marknzl/RoboticsYear13/3D Designs/models/Pallet.SLDPRT

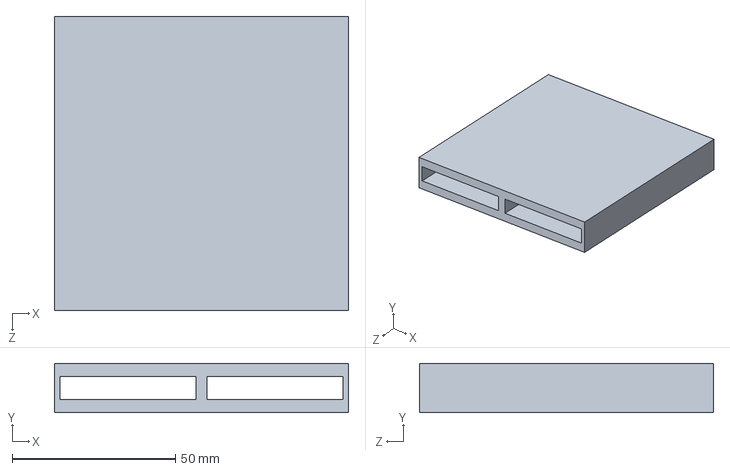
[picture p22: CAD file, 2021-07-02]
3D Designs/models/Pallet.SLDPRT
90.0 x 15.0 x 90.0 mm
