marknzl/RoboticsYear13/3D Designs/models/Pulley mount.SLDPRT

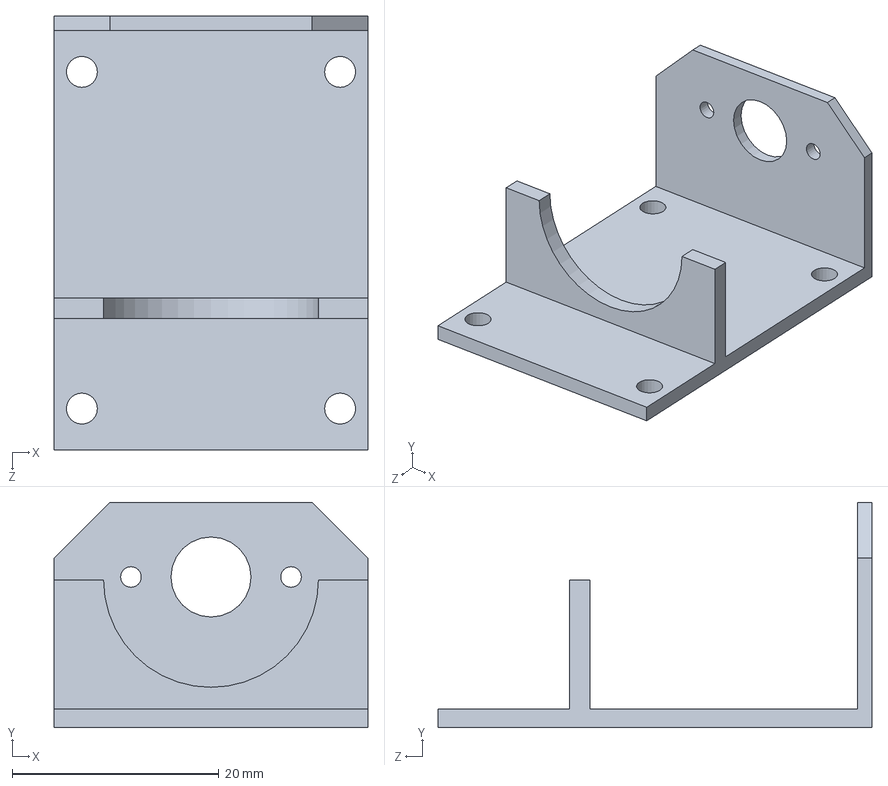
[picture p23: CAD file, 2021-07-02]
3D Designs/models/Pulley mount.SLDPRT
30.4 x 21.8 x 42.0 mm
