marknzl/RoboticsYear13/3D Designs/models/Motor.SLDPRT

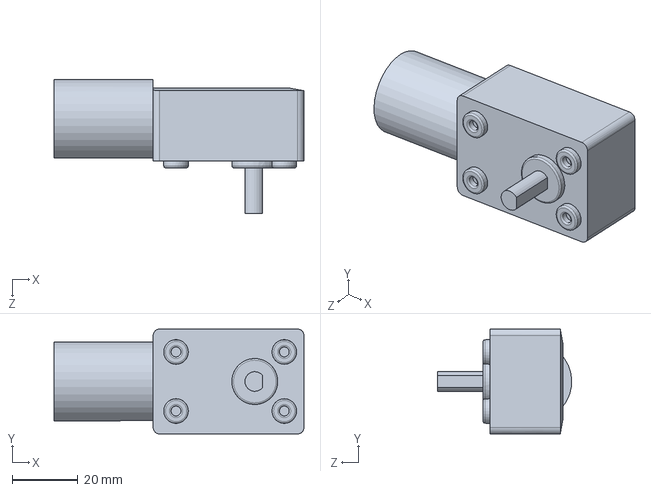
[picture p24: CAD file, 2021-07-02]
3D Designs/models/Motor.SLDPRT
76.2 x 32.0 x 41.0 mm
