marknzl/RoboticsYear13/3D Designs/models/Limit switch trigger.SLDPRT

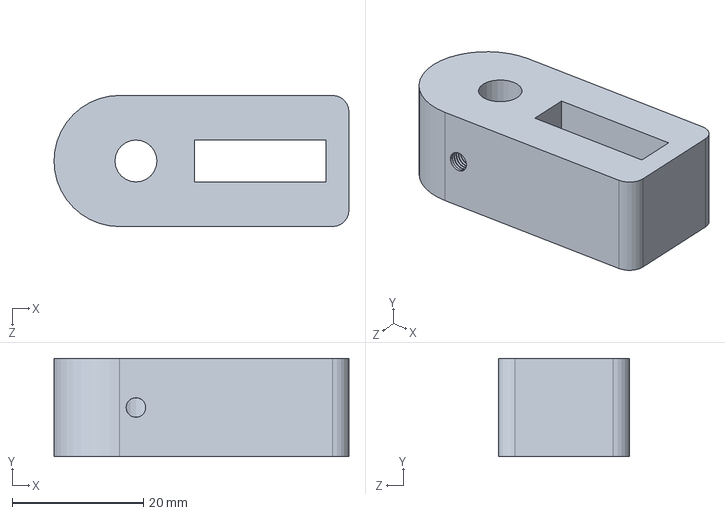
[picture p25: CAD file, 2021-07-02]
3D Designs/models/Limit switch trigger.SLDPRT
45.0 x 15.0 x 20.0 mm
