marknzl/RoboticsYear13/3D Designs/models/Timing belt fastener.SLDPRT

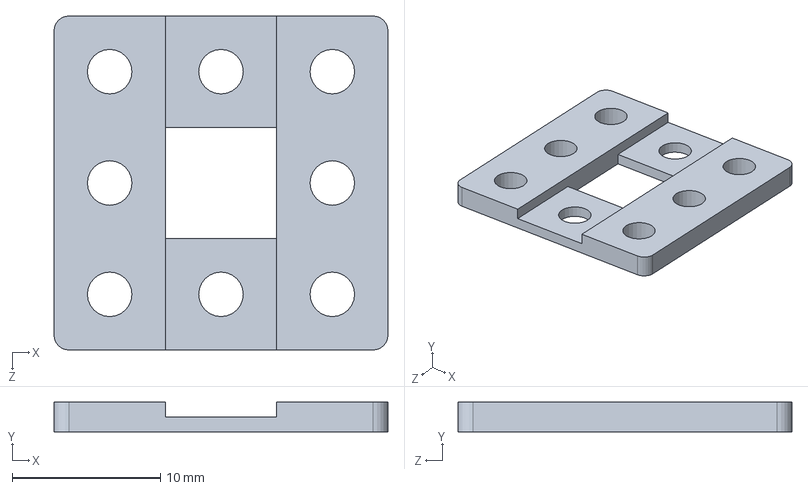
[picture p26: CAD file, 2021-07-02]
3D Designs/models/Timing belt fastener.SLDPRT
22.5 x 2.00 x 22.5 mm
