marknzl/RoboticsYear13/3D Designs/models/Motor clip - left (New).SLDPRT

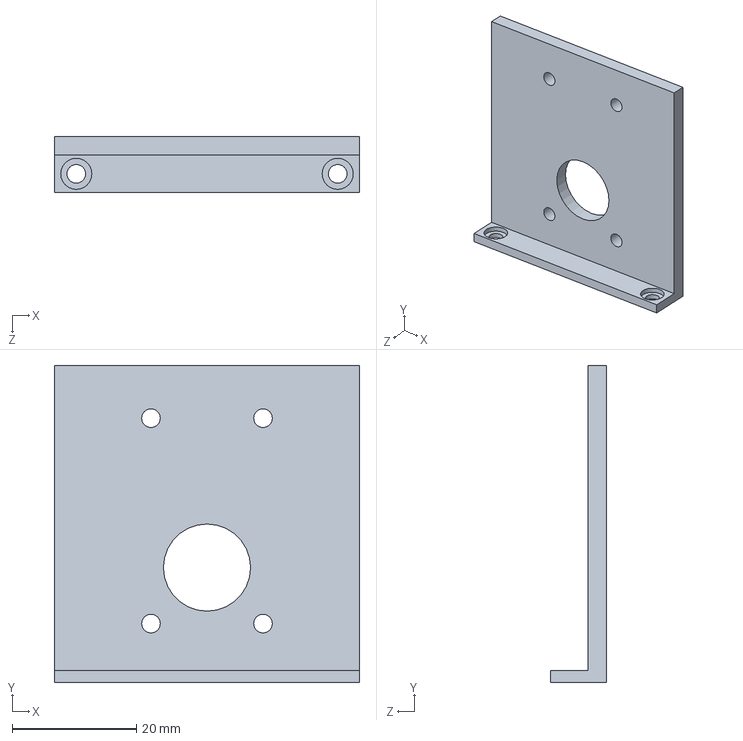
[picture p27: CAD file, 2021-07-02]
3D Designs/models/Motor clip - left (New).SLDPRT
49.0 x 51.0 x 9.00 mm
