marknzl/RoboticsYear13/3D Designs/models/Wheel (New).SLDPRT

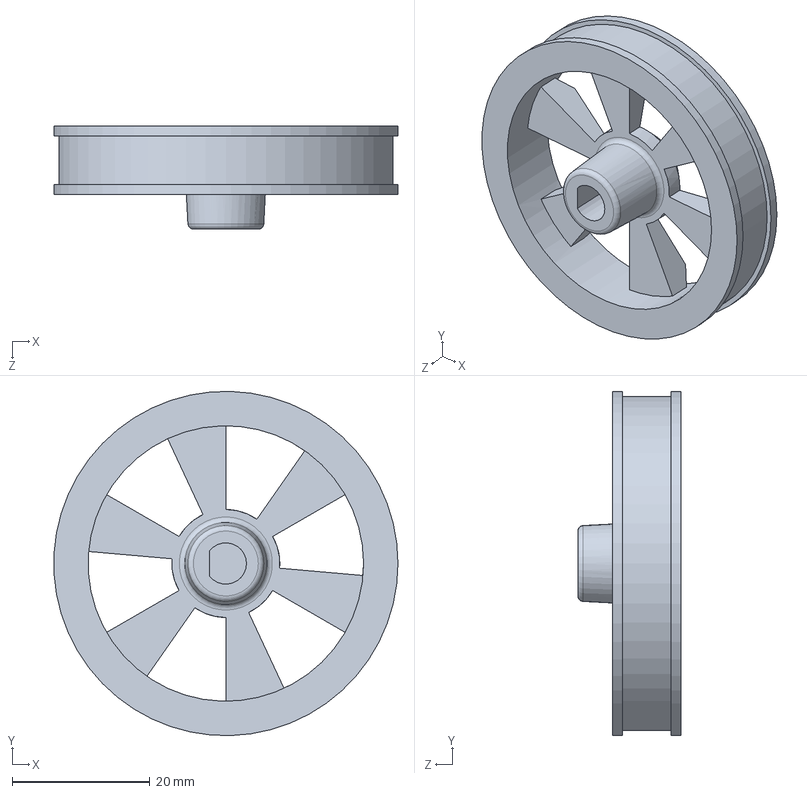
[picture p28: CAD file, 2021-07-02]
3D Designs/models/Wheel (New).SLDPRT
50.0 x 50.0 x 15.0 mm
