marknzl/RoboticsYear13/3D Designs/models/Arduino mount - Newest  (no mount).SLDPRT

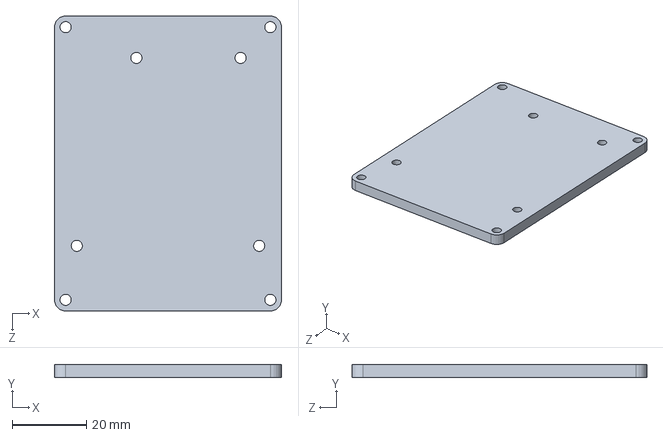
[picture p29: CAD file, 2021-07-02]
3D Designs/models/Arduino mount - Newest (no mount).SLDPRT
61.0 x 3.50 x 79.2 mm
