marknzl/RoboticsYear13/3D Designs/models/Standoff.SLDPRT

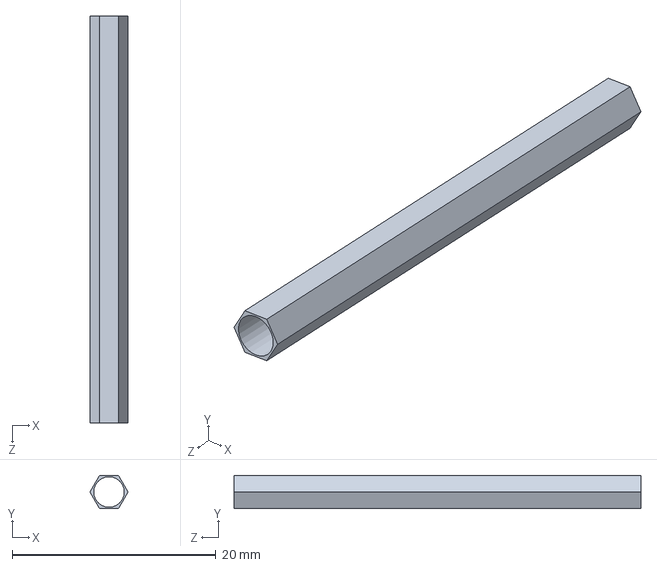
[picture p30: CAD file, 2021-07-02]
3D Designs/models/Standoff.SLDPRT
3.75 x 3.25 x 40.0 mm
