marknzl/RoboticsYear13/3D Designs/models/Limit switch.SLDPRT

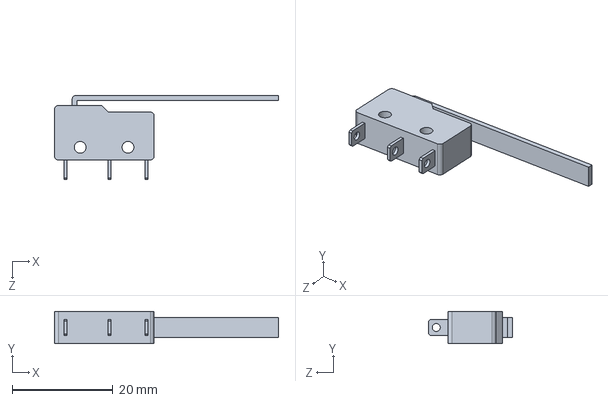
[picture p31: CAD file, 2021-07-02]
3D Designs/models/Limit switch.SLDPRT
44.5 x 6.40 x 16.7 mm
