marknzl/RoboticsYear13/3D Designs/models/Arduino mount - New.SLDPRT

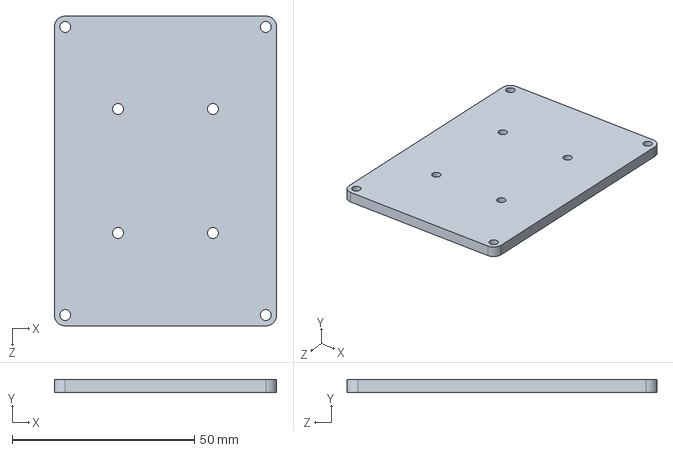
[picture p32: CAD file, 2021-07-02]
3D Designs/models/Arduino mount - New.SLDPRT
61.0 x 3.50 x 85.0 mm
