marknzl/RoboticsYear13/3D Designs/models/Pulley (new).SLDPRT

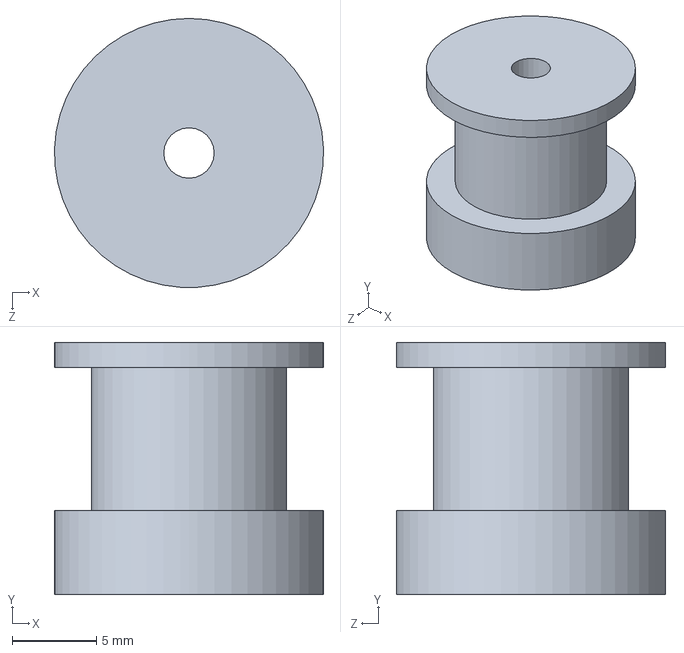
[picture p33: CAD file, 2021-07-02]
3D Designs/models/Pulley (new).SLDPRT
16.0 x 15.0 x 16.0 mm
