marknzl/RoboticsYear13/3D Designs/models/Pulley motor.SLDPRT

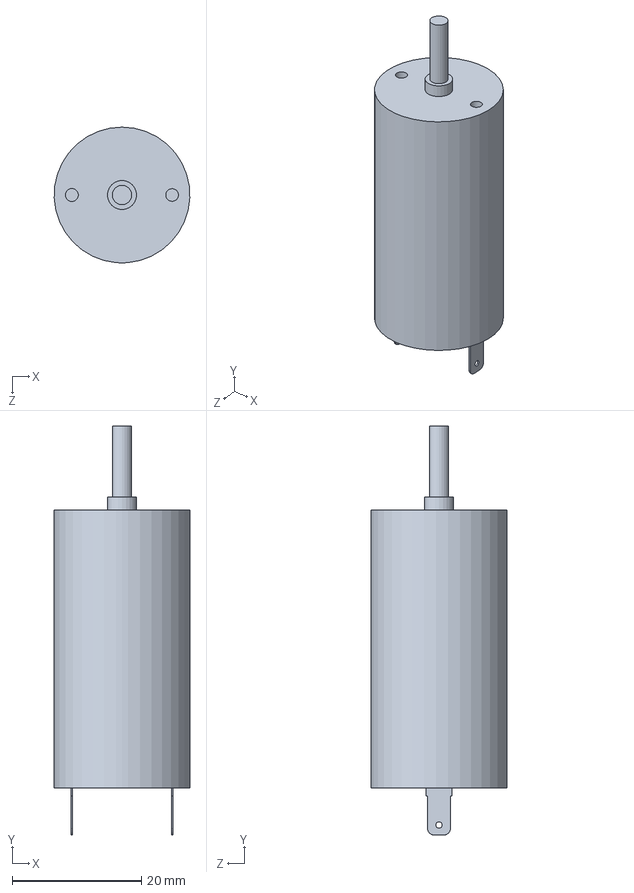
[picture p34: CAD file, 2021-07-02]
3D Designs/models/Pulley motor.SLDPRT
21.0 x 63.2 x 21.0 mm
