marknzl/RoboticsYear13/3D Designs/models/Pole.SLDPRT

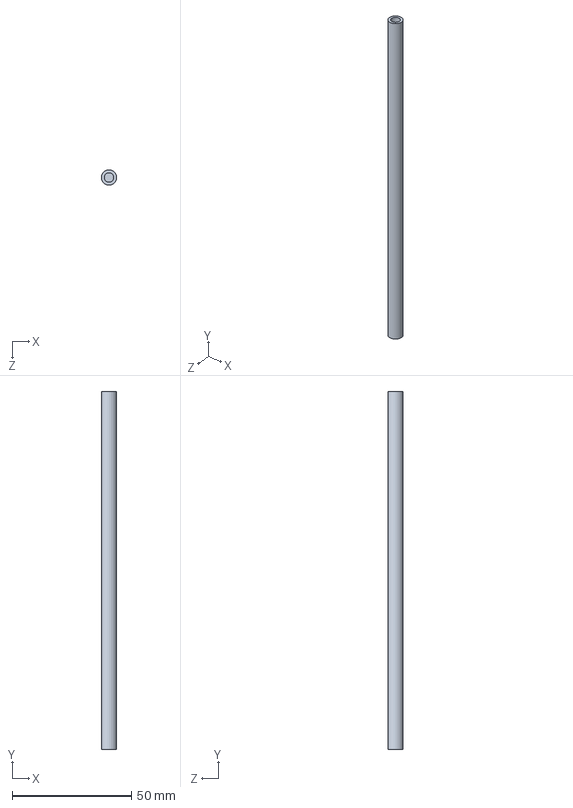
[picture p35: CAD file, 2021-07-02]
3D Designs/models/Pole.SLDPRT
6.40 x 150.0 x 6.40 mm
