marknzl/RoboticsYear13/3D Designs/models/Pallet (New v3).SLDPRT

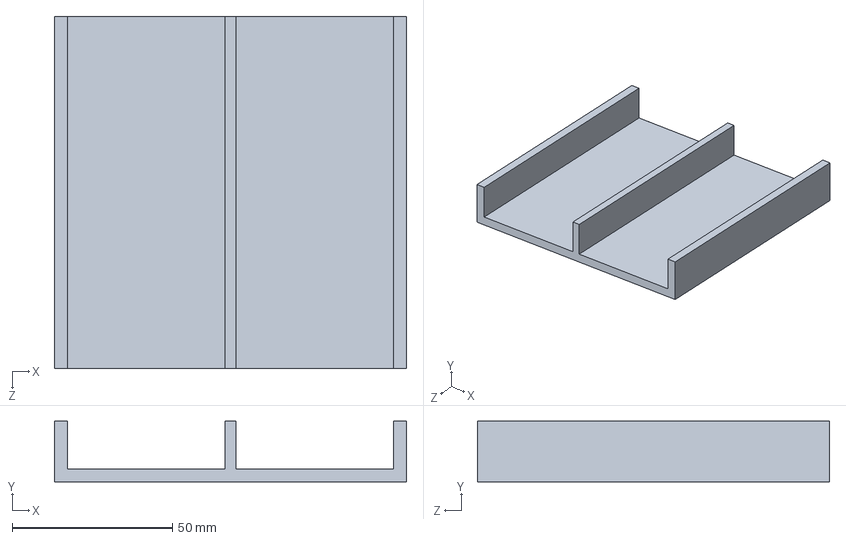
[picture p36: CAD file, 2021-07-02]
3D Designs/models/Pallet (New v3).SLDPRT
110.0 x 19.0 x 110.0 mm
