marknzl/RoboticsYear13/3D Designs/models/Forklift - Moving (New v5).SLDPRT

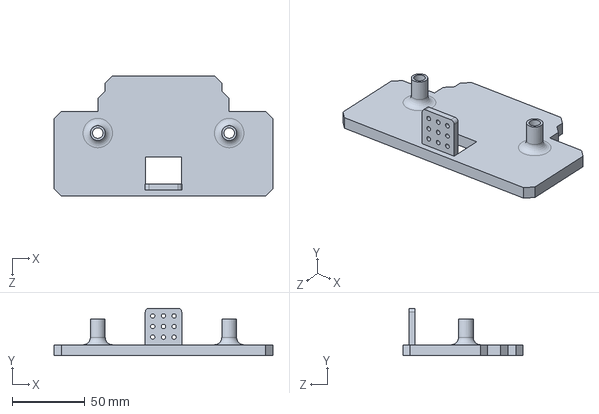
[picture p37: CAD file, 2021-07-02]
3D Designs/models/Forklift - Moving (New v5).SLDPRT
150.0 x 32.5 x 82.3 mm
