marknzl/RoboticsYear13/3D Designs/models/Arduino Uno R3.SLDPRT

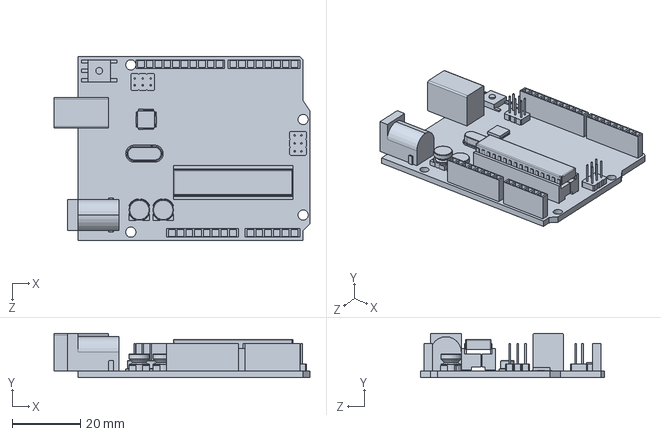
[picture p39: CAD file, 2021-07-02]
3D Designs/models/Arduino Uno R3.SLDPRT
75.0 x 13.0 x 54.0 mm
