marknzl/RoboticsYear13/3D Designs/models/Forklift - Moving.SLDPRT

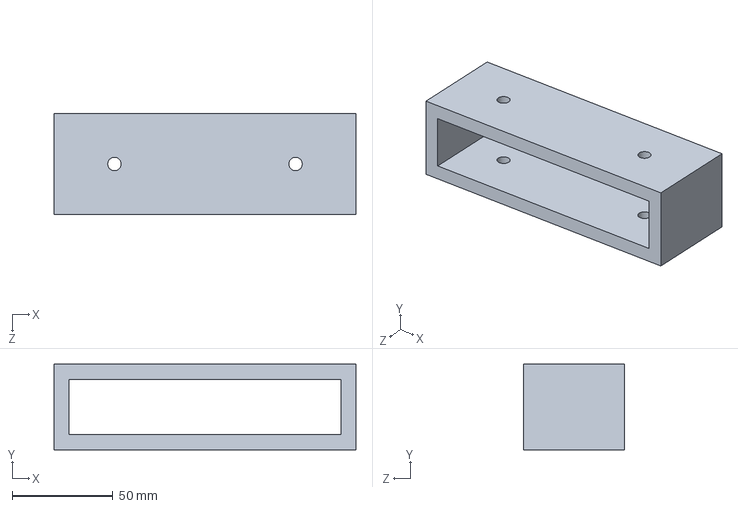
[picture p40: CAD file, 2021-07-02]
3D Designs/models/Forklift - Moving.SLDPRT
150.0 x 42.5 x 50.0 mm
