marknzl/RoboticsYear13/3D Designs/models/Forklift - Top (New v2).SLDPRT

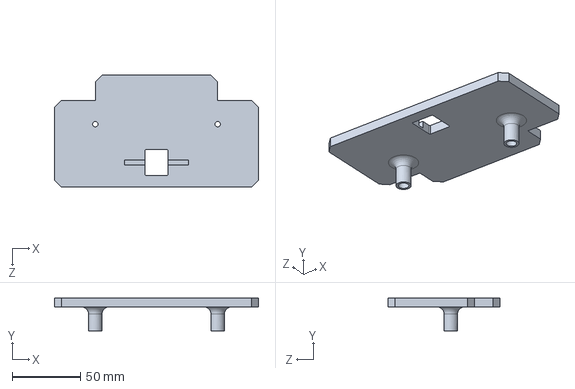
[picture p41: CAD file, 2021-07-02]
3D Designs/models/Forklift - Top (New v2).SLDPRT
150.0 x 24.0 x 82.3 mm
