marknzl/RoboticsYear13/3D Designs/models/Cylinder.SLDPRT

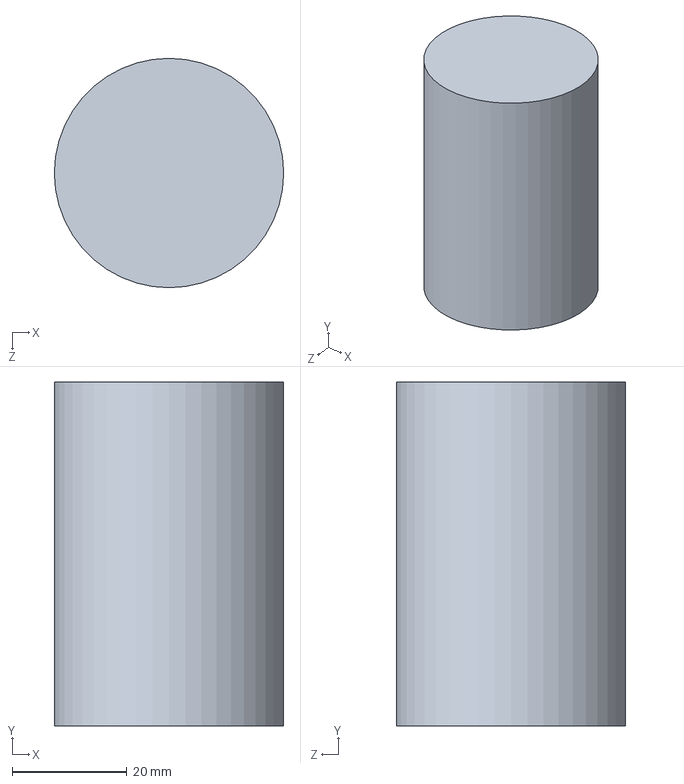
[picture p42: CAD file, 2021-07-02]
3D Designs/models/Cylinder.SLDPRT
40.0 x 60.0 x 40.0 mm
