marknzl/RoboticsYear13/3D Designs/models/Batter pack.SLDPRT

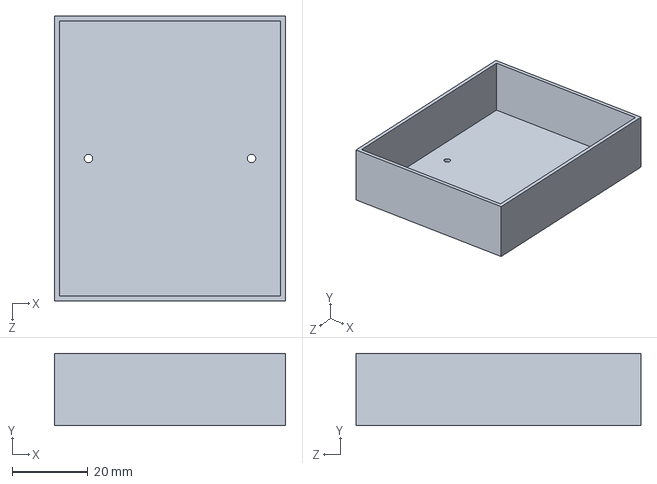
[picture p43: CAD file, 2021-07-02]
3D Designs/models/Batter pack.SLDPRT
61.2 x 19.1 x 75.5 mm
