marknzl/RoboticsYear13/3D Designs/models/Forklift - Front (v2).SLDPRT

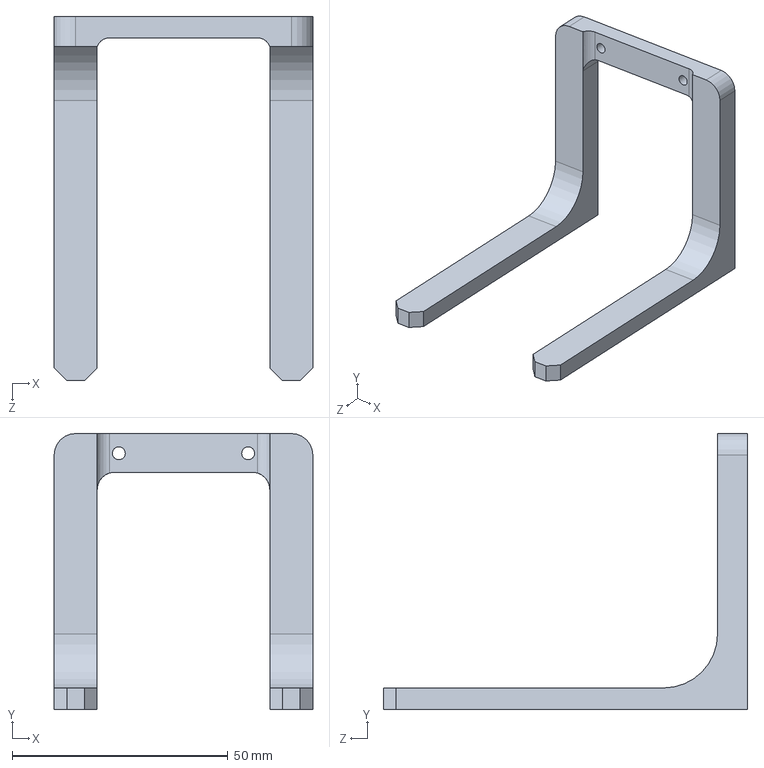
[picture p44: CAD file, 2021-07-02]
3D Designs/models/Forklift - Front (v2).SLDPRT
60.0 x 64.0 x 84.5 mm
