marknzl/RoboticsYear13/3D Designs/models/Forklift - Top.SLDPRT

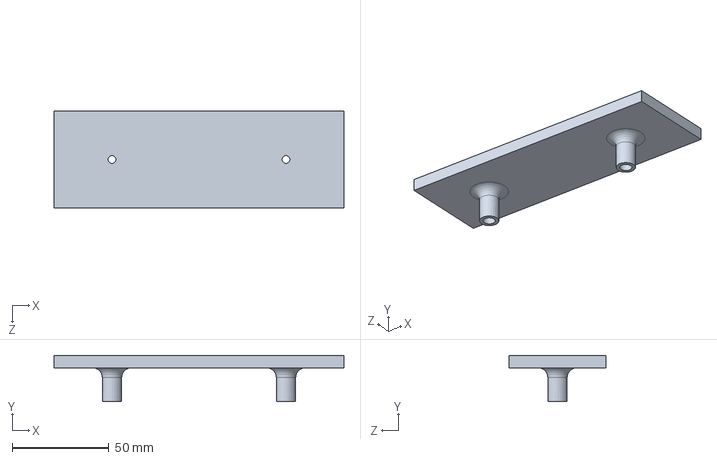
[picture p45: CAD file, 2021-07-02]
3D Designs/models/Forklift - Top.SLDPRT
150.0 x 24.0 x 50.0 mm
