marknzl/RoboticsYear13/3D Designs/models/Arduino holder - custom.SLDPRT

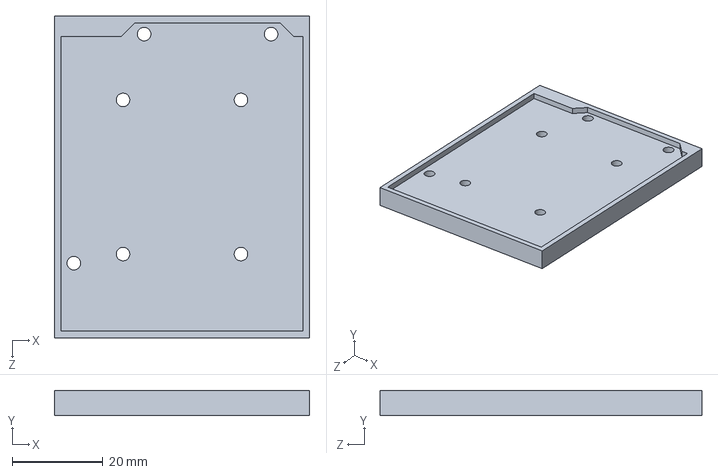
[picture p46: CAD file, 2021-07-02]
3D Designs/models/Arduino holder - custom.SLDPRT
56.3 x 5.60 x 71.0 mm
